prometheus-science/Automated-mouse-homecage-two-bottle-choice-test-v2/code/SipCounter-100618stable/SipCounter-100618stable/Logdata.ino

void LogData() {
  if (PongActive == false) {
    if (logReady == true) {
      Blink(RED_LED, 50, 3);  //blink while logging
      WriteToSD();
      logReady = false;
      logtimer = elapsed;
      logfile.flush();
    }
  }
}
// Create new file on uSD incrementing file name as required
void CreateFile() {
  //put this next line *Right Before* any file open line:
  SdFile::dateTimeCallback(dateTime);

  // see if the card is present and can be initialized:
  if (!SD.begin(cardSelect)) {
    error(2);
  }

  configfile = SD.open("DeviceNumber.csv", FILE_WRITE);

  // grab Sipper name from SipConfig.csv
  configfile = SD.open("DeviceNumber.csv", FILE_READ);
  Sip = configfile.parseInt();
  configfile.close();

  // Name filename in format F###_MMDDYYNN, where MM is month, DD is day, YY is year, and NN is an incrementing number for the number of files initialized each day
  strcpy(filename, "SIP_____________.CSV");  // placeholder filename
  getFilename(filename);

  logfile = SD.open(filename, FILE_WRITE);

  if ( ! logfile ) {
    error(3);
  }
}

// Write data header to file of uSD.
void writeHeader() {
  logfile.println("MM:DD:YYYY hh:mm:ss, Elapsed Time, Device, LeftCount, LeftDuration, RightCount, RightDuration, BatteryVoltage");
}

void writeConfigFile() {
  configfile = SD.open("DeviceNumber.csv", FILE_WRITE);
  configfile.rewind();
  configfile.println(Sip);
  configfile.close();
}

// Write data to SD
void WriteToSD() {
  logfile.print(rtc.getMonth());
  logfile.print("/");
  logfile.print(rtc.getDay());
  logfile.print("/");
  logfile.print(rtc.getYear() + 2000);
  logfile.print(" ");
  logfile.print(rtc.getHours());
  logfile.print(":");
  if (rtc.getMinutes() < 10)
    logfile.print('0');      // Trick to add leading zero for formatting
  logfile.print(rtc.getMinutes());
  logfile.print(":");
  if (rtc.getSeconds() < 10)
    logfile.print('0');      // Trick to add leading zero for formatting
  logfile.print(rtc.getSeconds());
  logfile.print(",");
  logfile.print(runHours); //elapsed time
  logfile.print(":");
  logfile.print(runMinutes); //elapsed time
  logfile.print(":");
  logfile.print(runSeconds); //elapsed time
  logfile.print(",");
  logfile.print(Sip); // Print device name
  logfile.print(",");
  logfile.print(LeftCount);
  logfile.print(",");
  logfile.print(LeftDuration);
  logfile.print(",");
  logfile.print(RightCount);
  logfile.print(",");
  logfile.print(RightDuration);
  logfile.print(",");
  logfile.println(measuredvbat); // Print battery voltage
}

void error(uint8_t errno) {
  while (1) {
    uint8_t i;
    for (i = 0; i < errno; i++) {
      DisplaySDError();
    }
  }
}

void getFilename(char *filename) {
  filename[3] = (Sip / 100) % 10 + '0';
  filename[4] = (Sip / 10) % 10 + '0';
  filename[5] = Sip % 10 + '0';
  filename[7] = rtc.getMonth() / 10 + '0';
  filename[8] = rtc.getMonth() % 10 + '0';
  filename[9] = rtc.getDay() / 10 + '0';
  filename[10] = rtc.getDay() % 10 + '0';
  filename[11] = rtc.getYear() / 10 + '0';
  filename[12] = rtc.getYear() % 10 + '0';
  filename[16] = '.';
  filename[17] = 'C';
  filename[18] = 'S';
  filename[19] = 'V';
  for (uint8_t i = 0; i < 100; i++) {
    filename[14] = '0' + i / 10;
    filename[15] = '0' + i % 10;
    // create if does not exist, do not open existing, write, sync after write
    if (! SD.exists(filename)) {
      break;
    }
  }
  return;
}

void logtimerfunction() {
  if (elapsed - logtimer >= 10) {
    logReady = true;
  }
}

void calcTimeElapsed() {
  elapsed = ((millis() - startmillis) / 1000);
  runHours = elapsed / 3600;
  secsRemaining = elapsed % 3600;
  runMinutes = secsRemaining / 60;
  runSeconds = secsRemaining % 60;
}
